alicemirror/3DPrinterFilamentDispenserAndMonitor/images/IMG_20170629_110404.jpg

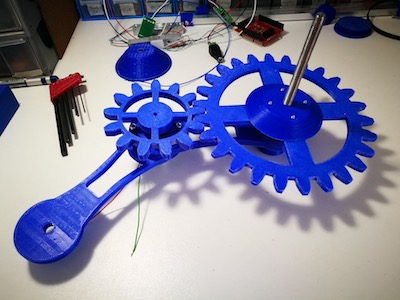
images/IMG_20170629_110404.jpg
