alicemirror/3DPrinterFilamentDispenserAndMonitor/images/IMG_20170701_140929.jpg

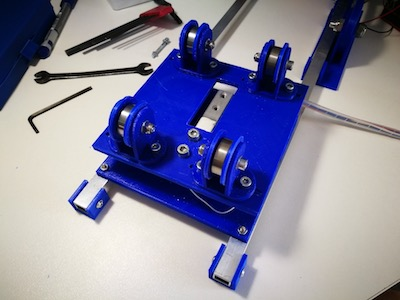
images/IMG_20170701_140929.jpg
