alicemirror/3DPrinterFilamentDispenserAndMonitor/images/IMG_20170705_222226.jpg

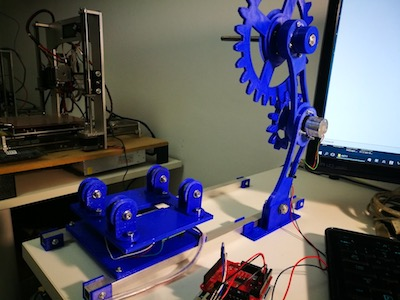
images/IMG_20170705_222226.jpg
