alicemirror/3DPrinterFilamentDispenserAndMonitor/STL/RollMotorSeparator.stl

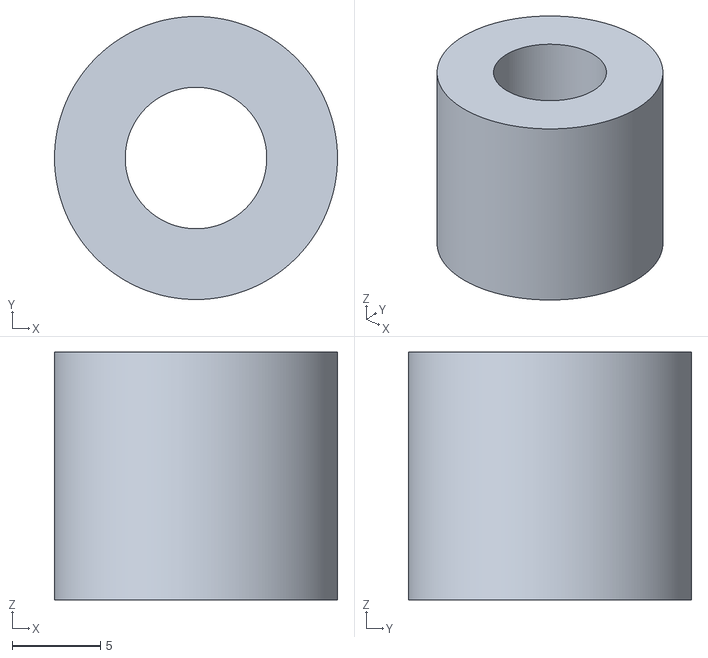
[picture p23: CAD file, 2018-04-11]
STL/RollMotorSeparator.stl
16.0 x 16.0 x 14.0
