alicemirror/3DPrinterFilamentDispenserAndMonitor/STL/RollMotorLockTop.stl

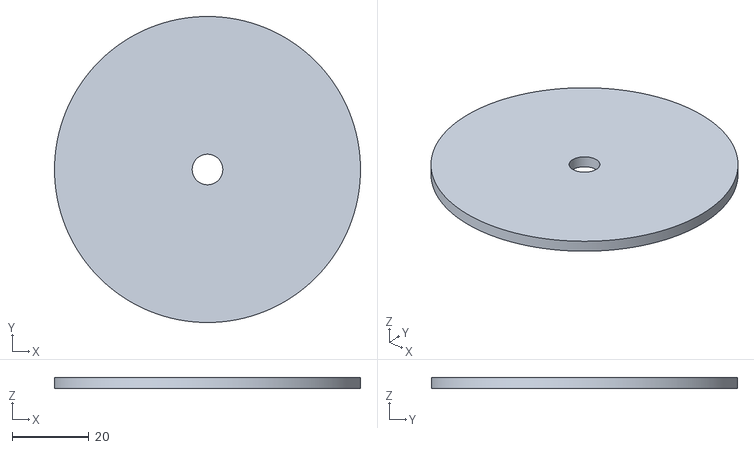
[picture p24: CAD file, 2018-04-11]
STL/RollMotorLockTop.stl
80.0 x 80.0 x 3.00
